pizzahack/mrcoffee/stl/side_plate_540200.stl

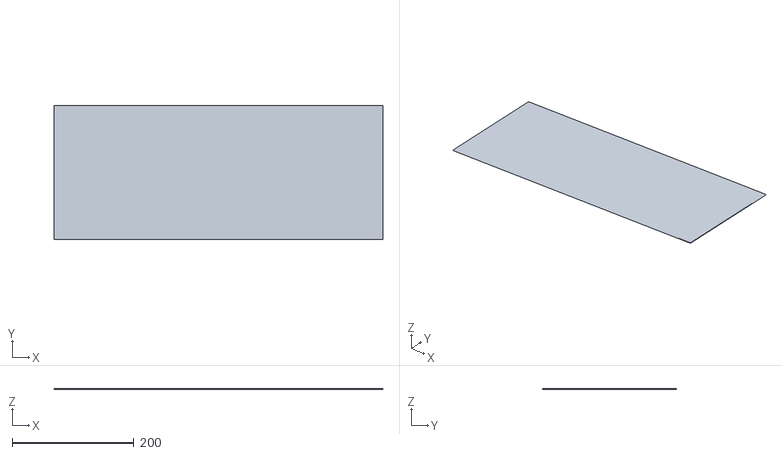
[picture p18: CAD file, 2021-05-26]
stl/side_plate_540200.stl
540.0 x 220.0 x 1.00
