pizzahack/mrcoffee/cad/test-motor-gear.FCStd

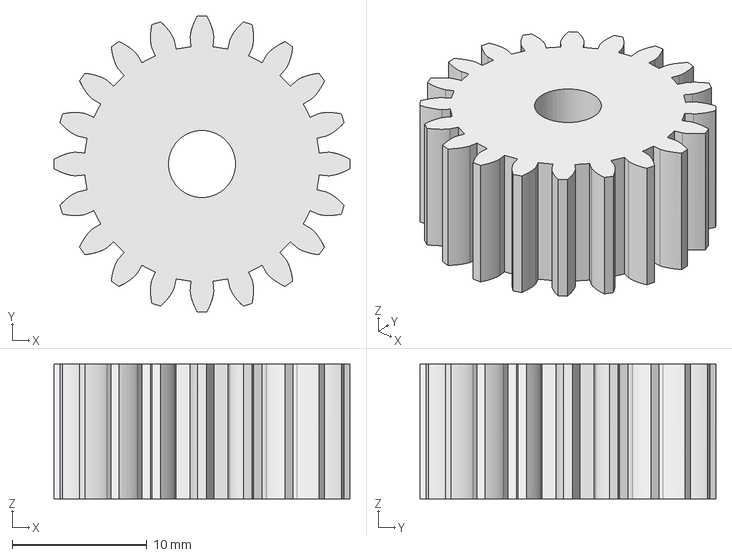
[picture p19: CAD file, 2024-06-23]
cad/test-motor-gear.FCStd
22.0 x 22.0 x 10.0 mm
