pizzahack/mrcoffee/cad/test-gear.FCStd

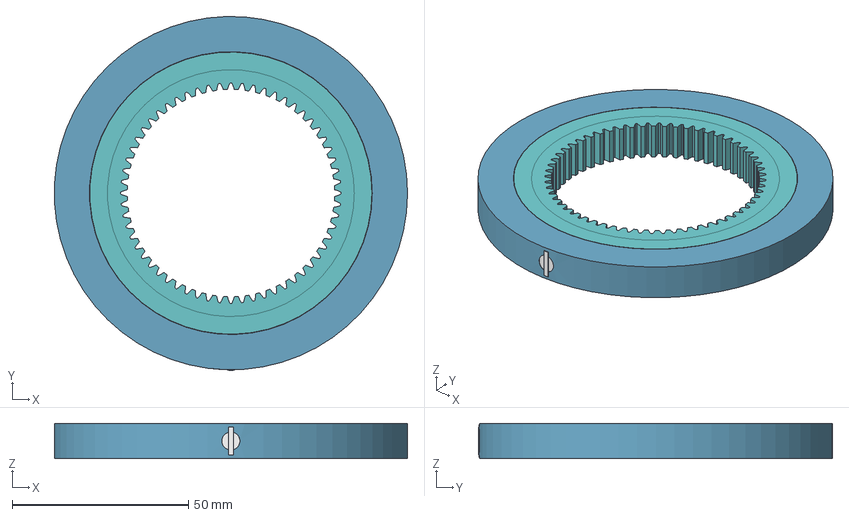
[picture p20: CAD file, 2024-06-23]
cad/test-gear.FCStd
100.1 x 100.4 x 10.0 mm
inner
outer
plug_w_butterfly
