pizzahack/mrcoffee/cad/base_2.0.FCStd

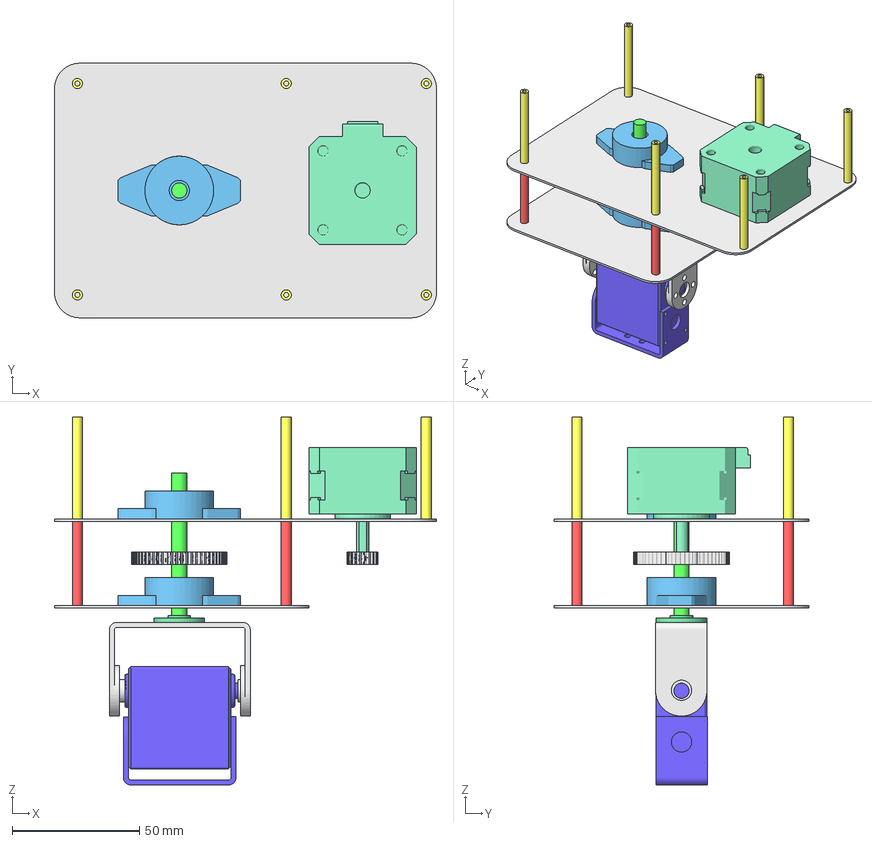
[picture p21: CAD file, 2024-01-14]
cad/base_2.0.FCStd
150.0 x 100.0 x 144.5 mm
gear_20T
gear_60T
bottom_plate
top_plate
shaft
spacer
spacer001
spacer002
spacer003
top_spacer
top_spacer001
top_spacer002
top_spacer003
top_spacer004
top_spacer005
NEMA_17_SLIM
servo_metal_disc
servo_with_small_bracket_for_gazebo
large_bracket_with_discs_for_gazebo
bottom_bearing
top_bearing
