pizzahack/mrcoffee/cad/mrcoffee.FCStd

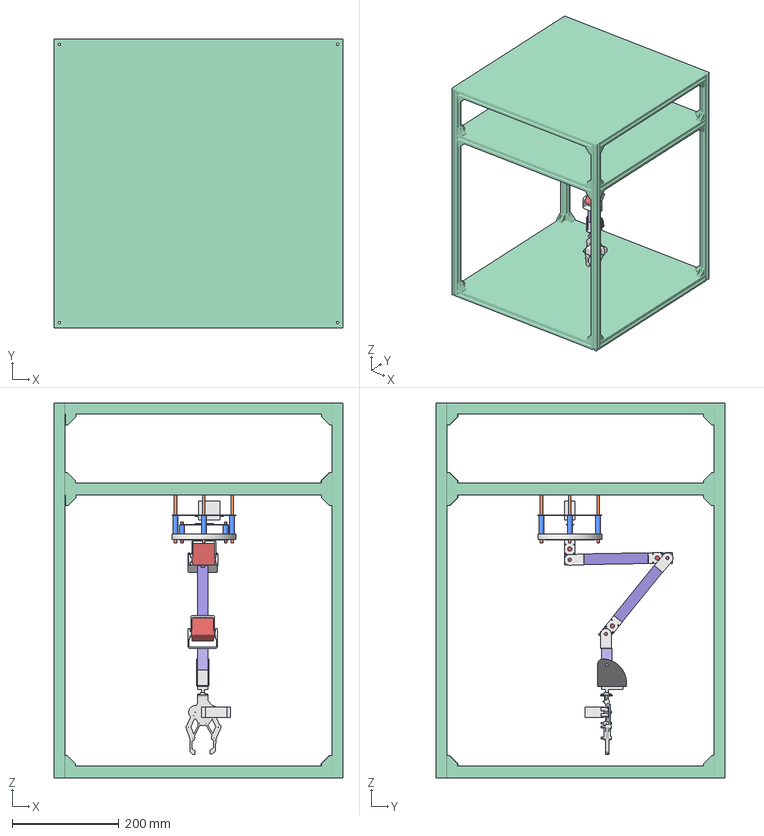
[picture p22: CAD file, 2024-01-14]
cad/mrcoffee.FCStd
540.0 x 540.0 x 701.0 mm
bearing
threaded_rod_long
threaded_rod_long001
threaded_rod_long002
threaded_rod_long003
long_spacer
threaded_rod_short
threaded_rod_short002
servo_horn
horn_bar
servo_holder003
arm_plate
long_spacer_2
long_spacer_3
long_spacer_4
short_spacer
short_spacer_2
wrist_servo_holder
wrist_servo_mg996r
base_servo_mg996r_360
gripper_servo_mg996r
large_bracket_with_discs_1
small_bracket_1
servo_270_20_1
robot_cage
small_bracket_2
servo_270_20_2
large_bracket_with_discs_2
aluminium_extrusion_2020_120
small_bracket_3
servo_270_20_3
large_bracket_with_discs_3
aluminium_extrusion_2020_120_2
servo_metal_disc_w_gear
aluminium_extrusion_2020_40
off-the-shelf_gripper
servo_metal_disc_w_gear001
