pizzahack/mrcoffee/cad/wrist_servo_holder.FCStd

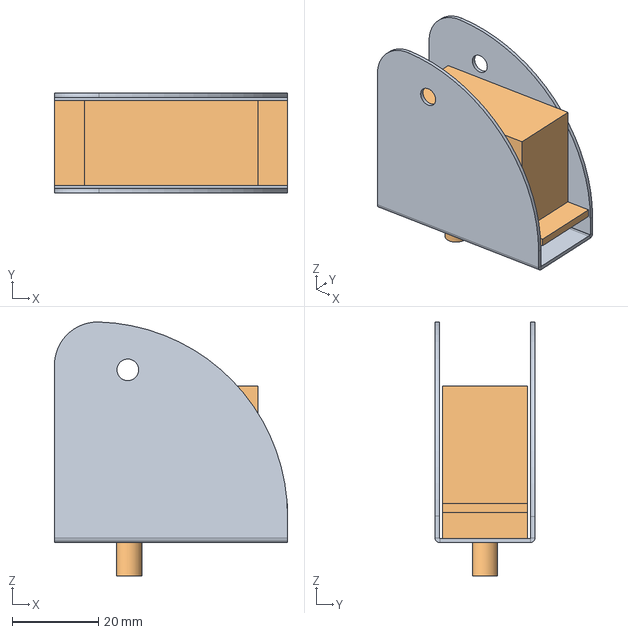
[picture p23: CAD file, 2024-01-14]
cad/wrist_servo_holder.FCStd
54.0 x 23.2 x 58.8 mm
wrist_servo_holder
wrist_servo
