pizzahack/mrcoffee/cad/gripper.FCStd

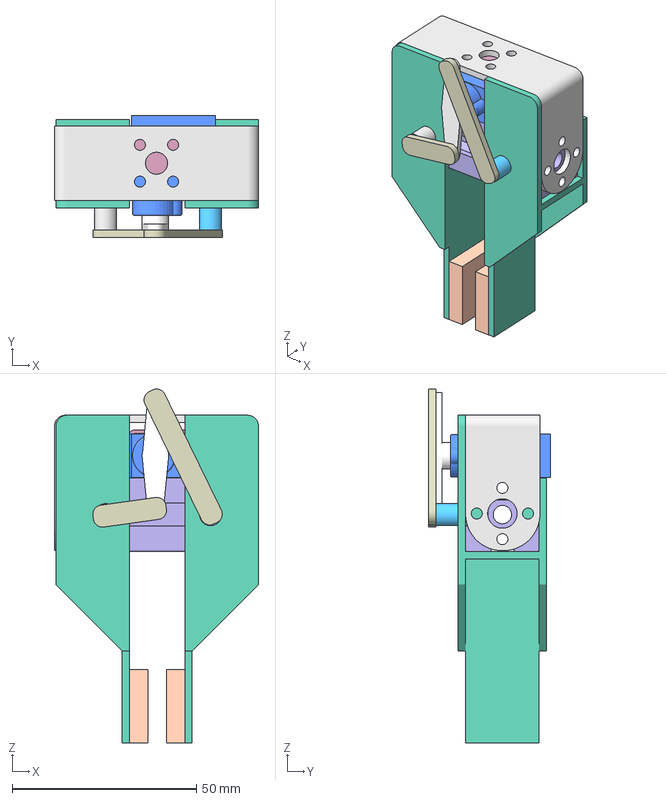
[picture p24: CAD file, 2022-01-14]
cad/gripper.FCStd
55.4 x 33.0 x 96.1 mm
gripper_pad_right
gripper_pad_left
horn_bar_1
horn_bar_2
horn_bar_spacer_1
horn_bar_spacer_002
gripper_pad_1
gripper_pad_2
servo_bracket
large_bracket
aluminium_extrusion_2020_55
servo_9g-servo
servo_9g-servo_horn
