pizzahack/mrcoffee/cad/base_with_servo.FCStd

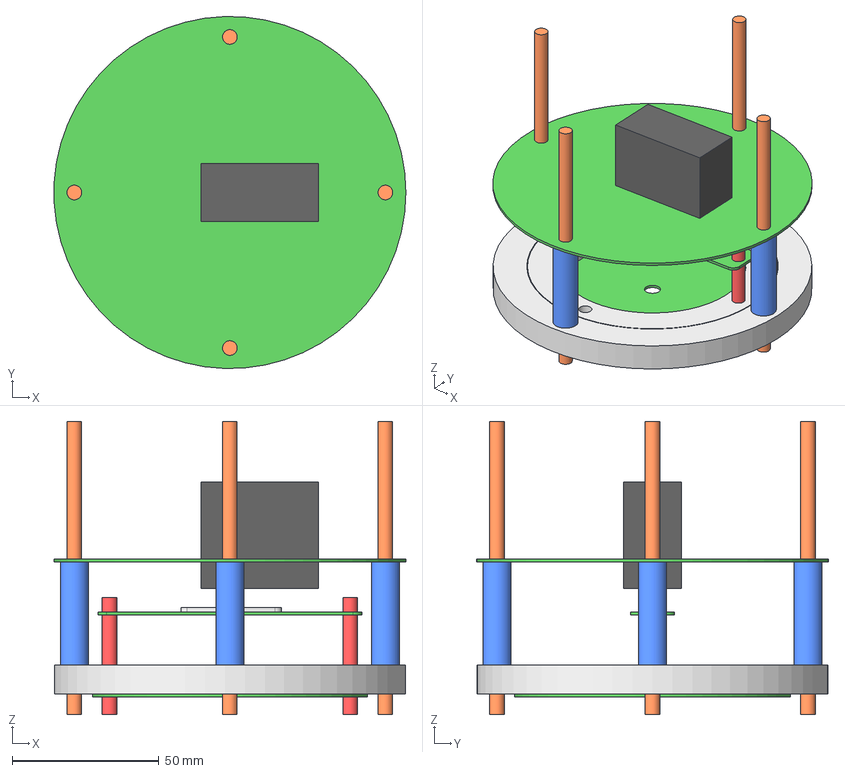
[picture p25: CAD file, 2021-12-29]
cad/base_with_servo.FCStd
119.9 x 120.0 x 100.0 mm
bearing
servo
threaded_rod_long
threaded_rod_long001
threaded_rod_long002
threaded_rod_long003
spacer
threaded_rod_short
threaded_rod_short002
servo_horn
horn_bar
servo_holder003
arm_plate
spacer001
spacer002
spacer003
