pizzahack/mrcoffee/cad/servo_9g_horn.FCStd

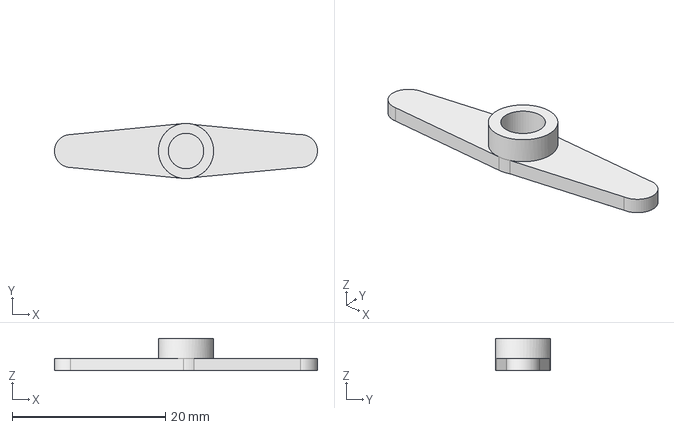
[picture p26: CAD file, 2021-09-16]
cad/servo_9g_horn.FCStd
34.3 x 7.20 x 4.23 mm
