pizzahack/mrcoffee/cad/servo_9g.FCStd

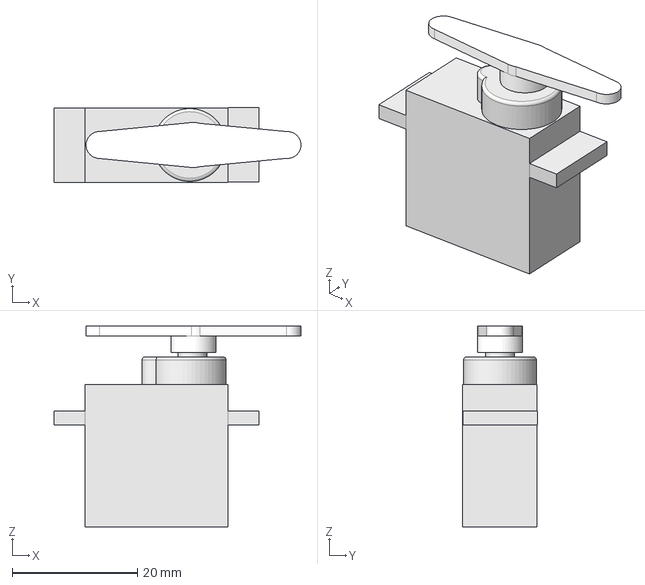
[picture p27: CAD file, 2021-09-16]
cad/servo_9g.FCStd
39.4 x 11.9 x 32.0 mm
servo
servo_horn
