pizzahack/mrcoffee/cad/power_supply_12V.FCStd

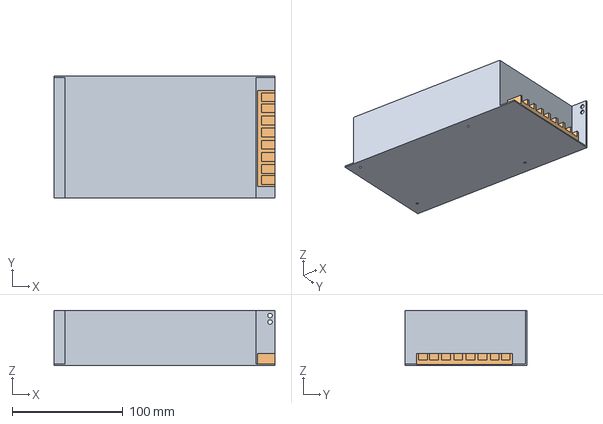
[picture p28: CAD file, 2021-09-03]
cad/power_supply_12V.FCStd
200.0 x 110.0 x 50.0 mm
