pizzahack/mrcoffee/cad/radiator.FCStd

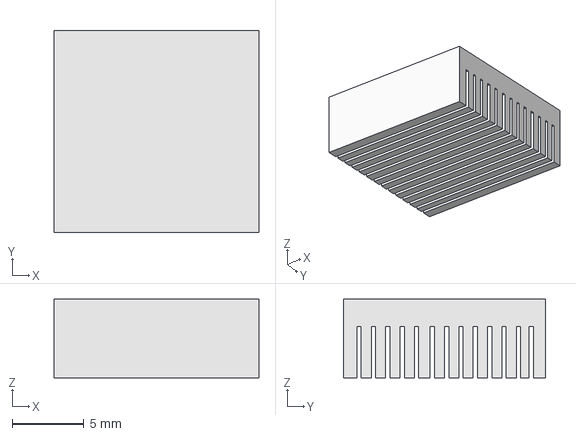
[picture p29: CAD file, 2021-09-03]
cad/radiator.FCStd
14.3 x 14.1 x 5.50 mm
