pizzahack/mrcoffee/cad/reley.FCStd

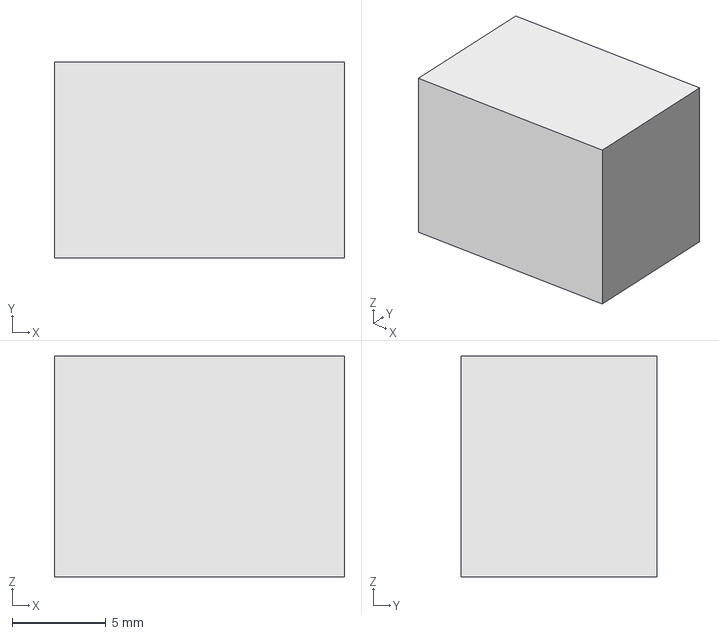
[picture p30: CAD file, 2021-08-31]
cad/reley.FCStd
15.5 x 10.5 x 11.8 mm
