pizzahack/mrcoffee/cad/blue_led.FCStd

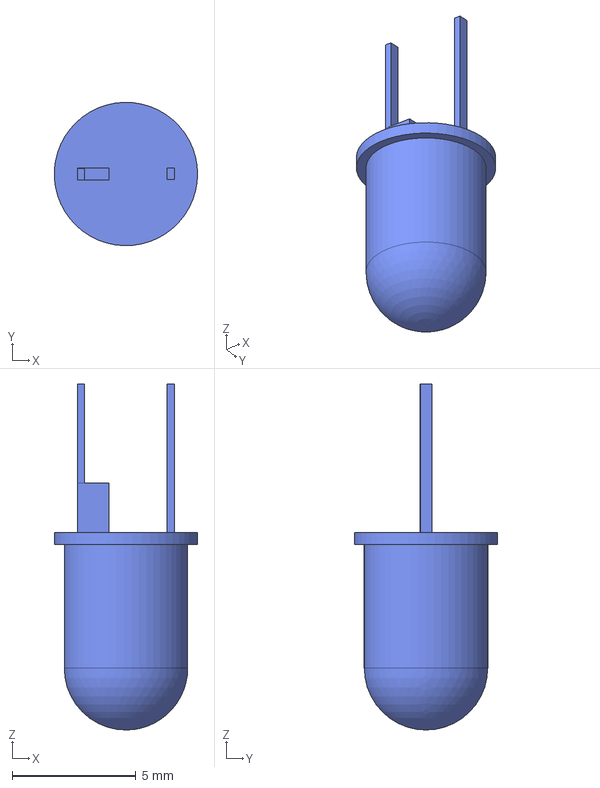
[picture p31: CAD file, 2021-08-31]
cad/blue_led.FCStd
5.79 x 5.80 x 14.0 mm
