pizzahack/mrcoffee/cad/led_pcb.FCStd

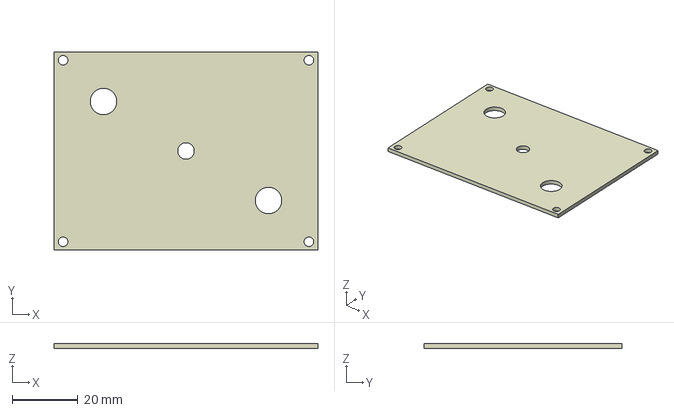
[picture p32: CAD file, 2021-08-30]
cad/led_pcb.FCStd
80.0 x 60.0 x 1.50 mm
