pizzahack/mrcoffee/cad/power_led.FCStd

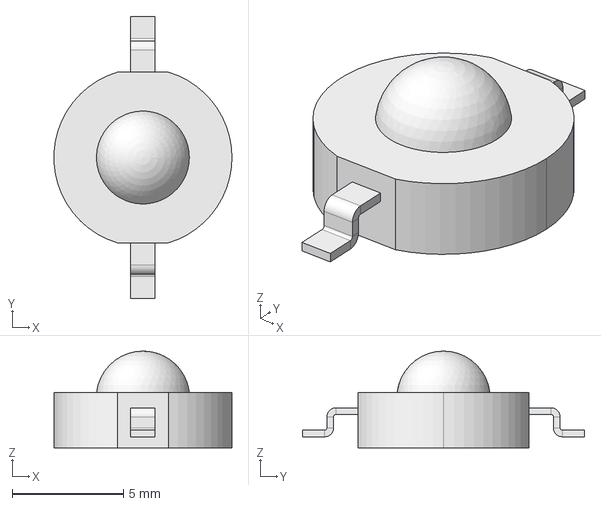
[picture p33: CAD file, 2021-08-30]
cad/power_led.FCStd
7.99 x 12.7 x 4.35 mm
