pizzahack/mrcoffee/cad/base_with_bearing.FCStd

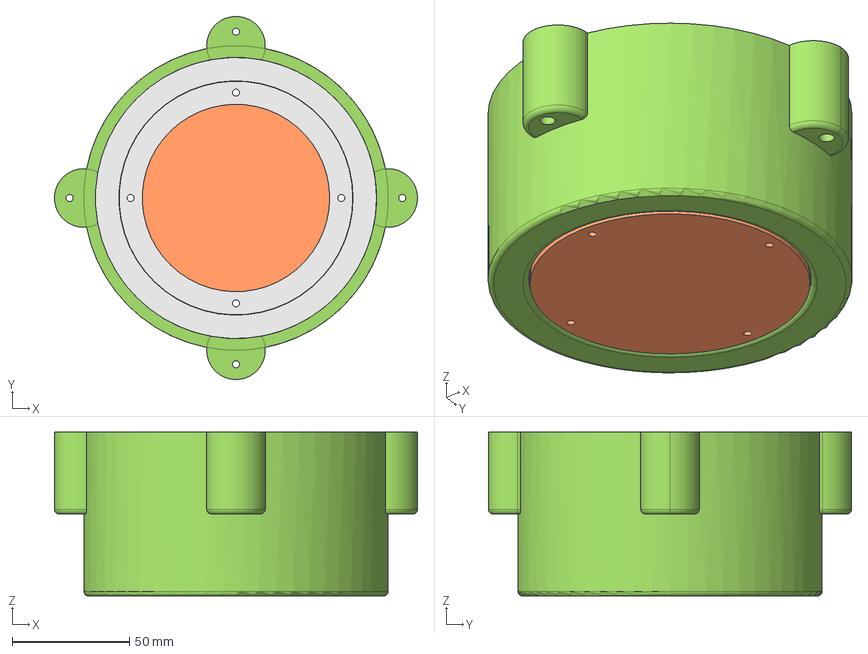
[picture p34: CAD file, 2021-07-19]
cad/base_with_bearing.FCStd
155.0 x 155.0 x 70.0 mm
outer_ring
inner_ring
base_holder
base_plate
