pizzahack/mrcoffee/cad/90_bracket.FCStd

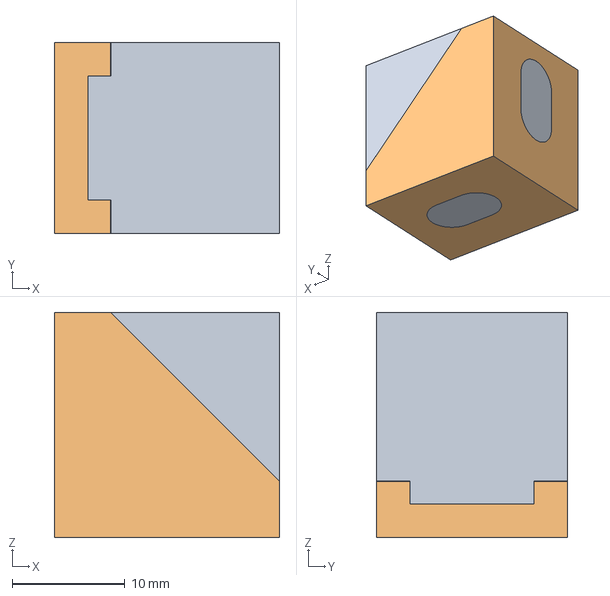
[picture p35: CAD file, 2021-06-07]
cad/90_bracket.FCStd
20.0 x 17.0 x 20.0 mm
