pizzahack/mrcoffee/cad/small_bracket.FCStd

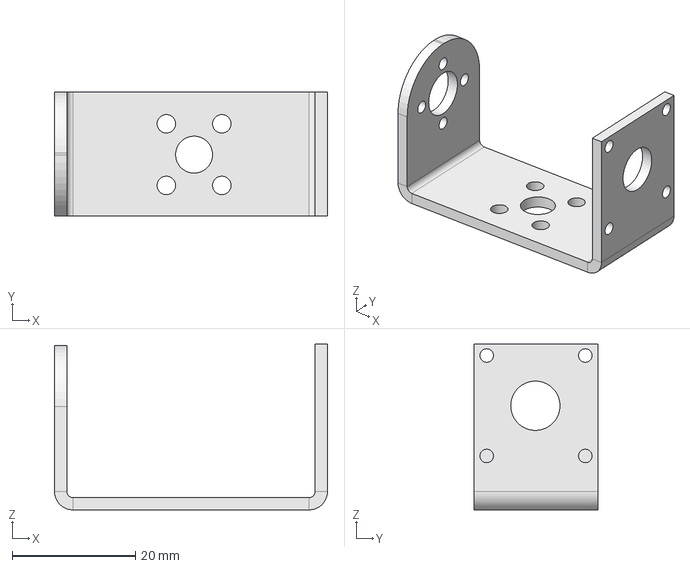
[picture p36: CAD file, 2021-06-02]
cad/small_bracket.FCStd
44.3 x 20.2 x 26.9 mm
