pizzahack/mrcoffee/cad/aluminium_extrusion_2020.FCStd

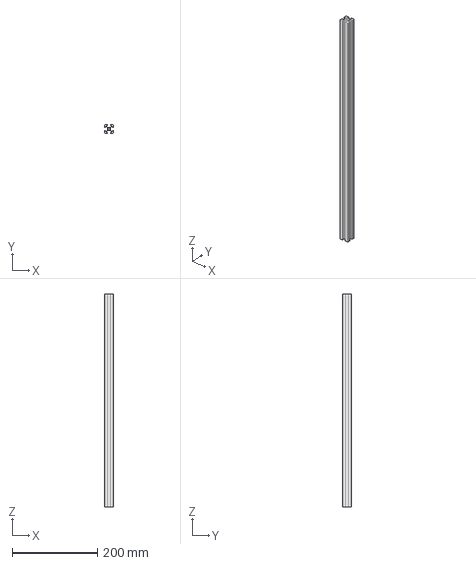
[picture p37: CAD file, 2021-06-02]
cad/aluminium_extrusion_2020.FCStd
20.0 x 20.0 x 500.0 mm
