pizzahack/mrcoffee/cad/large_bracket.FCStd

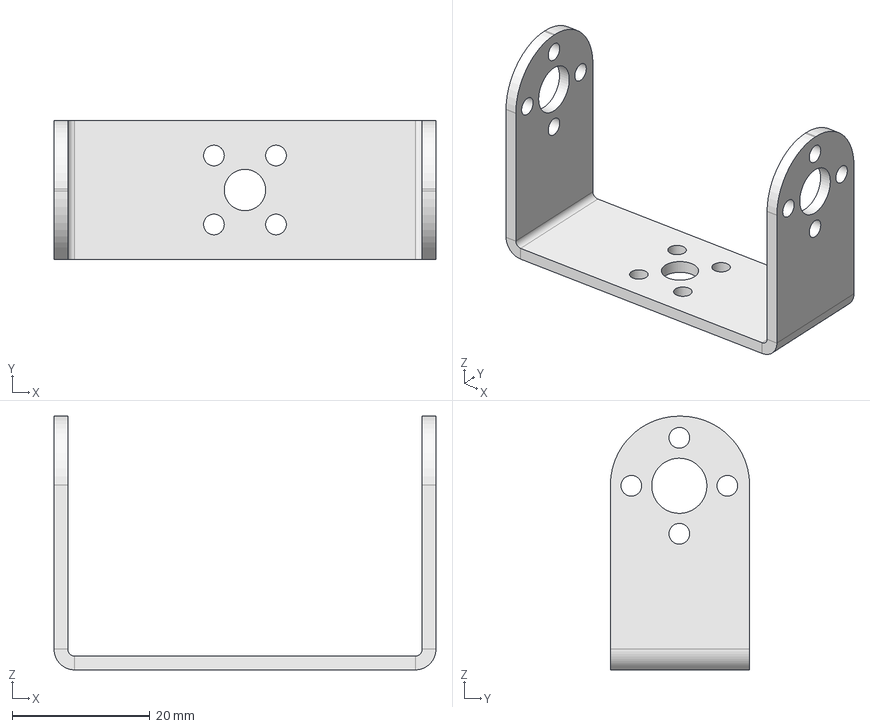
[picture p38: CAD file, 2021-06-02]
cad/large_bracket.FCStd
55.4 x 20.2 x 36.8 mm
