pizzahack/mrcoffee/cad/servo_270_20.FCStd

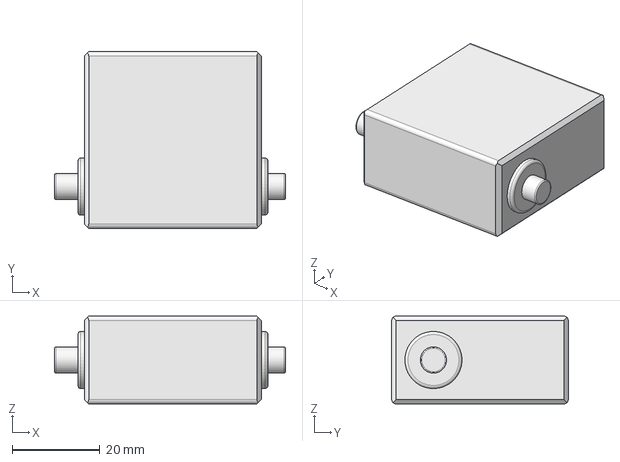
[picture p39: CAD file, 2021-06-01]
cad/servo_270_20.FCStd
52.6 x 40.2 x 20.0 mm
