pizzahack/mrcoffee/cad/servo_metal_disc.FCStd

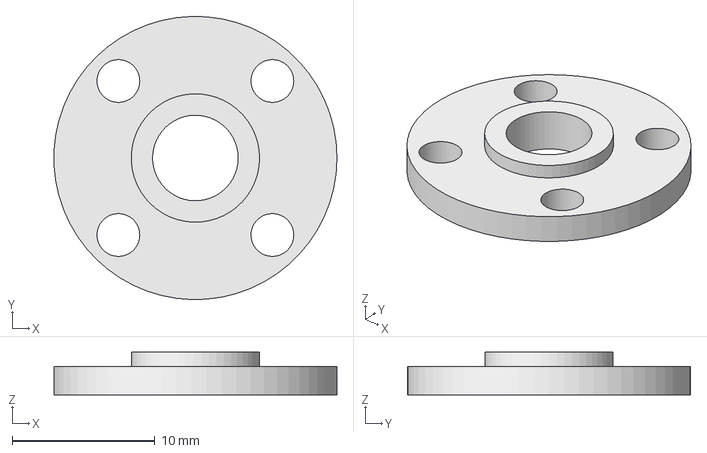
[picture p40: CAD file, 2021-05-30]
cad/servo_metal_disc.FCStd
19.8 x 19.9 x 3.00 mm
