pizzahack/mrcoffee/cad/top_middle_plate_500500.FCStd

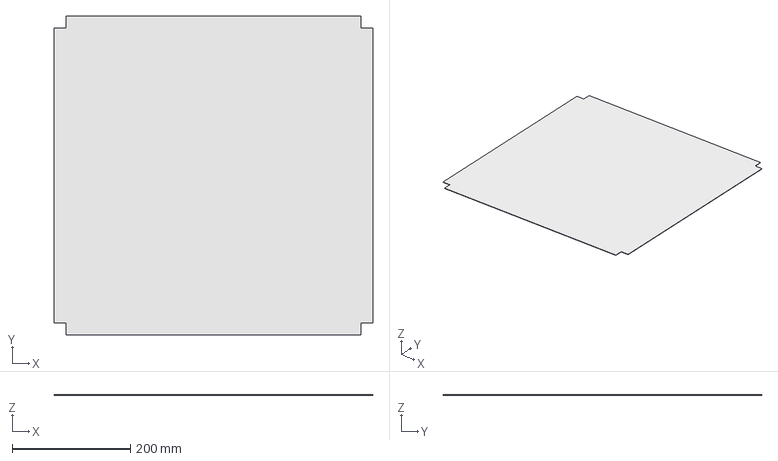
[picture p41: CAD file, 2021-05-26]
cad/top_middle_plate_500500.FCStd
540.0 x 540.0 x 1.00 mm
