pizzahack/mrcoffee/cad/top_plate_500500.FCStd

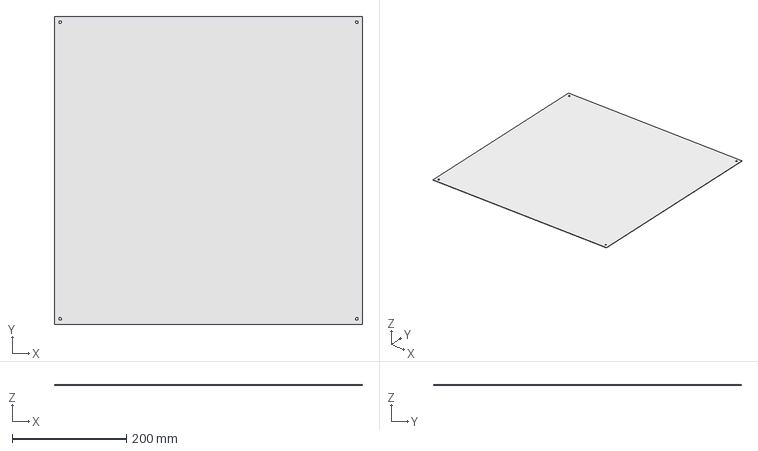
[picture p42: CAD file, 2021-05-26]
cad/top_plate_500500.FCStd
540.0 x 540.0 x 1.00 mm
