pizzahack/mrcoffee/cad/bottom_plate_500500.FCStd

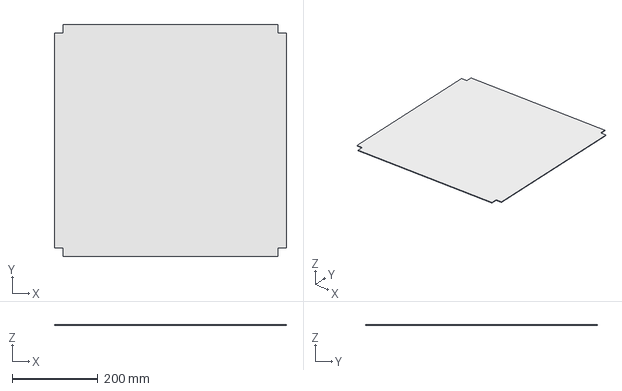
[picture p43: CAD file, 2021-05-26]
cad/bottom_plate_500500.FCStd
540.0 x 540.0 x 2.00 mm
