pizzahack/mrcoffee/cad/aluminium_extrusion_2020_700.FCStd

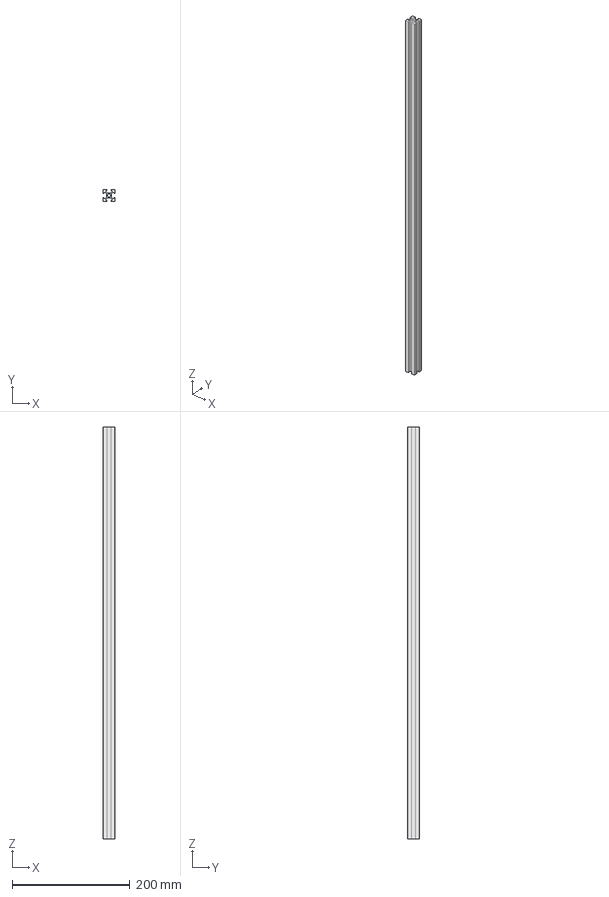
[picture p44: CAD file, 2021-05-24]
cad/aluminium_extrusion_2020_700.FCStd
20.0 x 20.0 x 700.0 mm
